sssata/fluxpad/APP/images/cal_key1_up.png

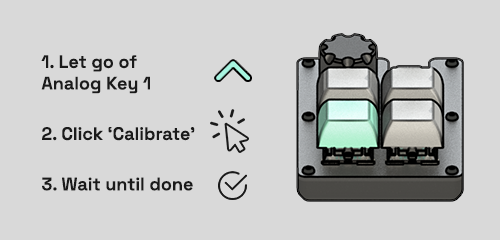
APP/images/cal_key1_up.png
