sssata/fluxpad/APP/images/cal_key2_down.png

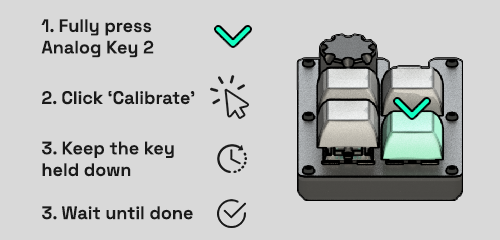
APP/images/cal_key2_down.png
