sssata/fluxpad/APP/images/cal_key2_up.png

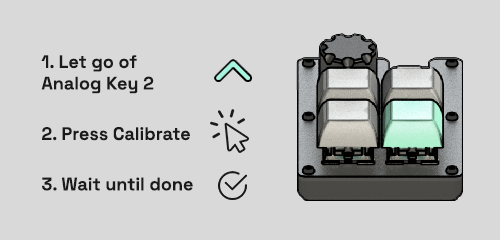
APP/images/cal_key2_up.png
