sssata/fluxpad/APP/images/cal_key3_down_2.png

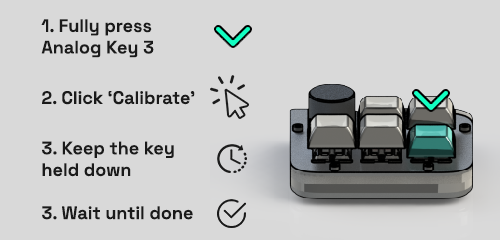
APP/images/cal_key3_down_2.png
