sssata/fluxpad/CAD/EE Export/302_PLATE.DXF

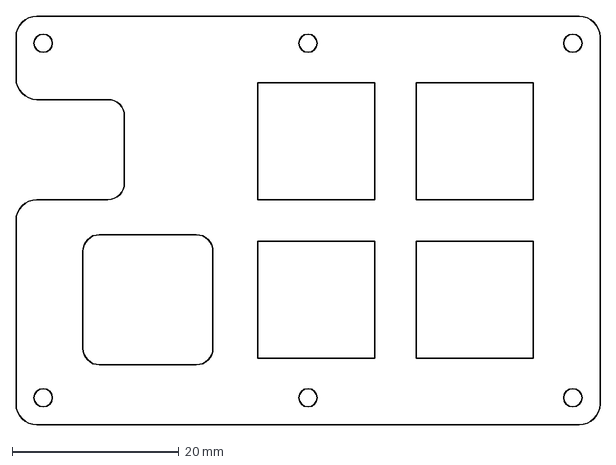
[picture p15: CAD file, 2023-02-28]
CAD/EE Export/302_PLATE.DXF
70.0 x 49.0 mm
