sssata/fluxpad/CAD/STL Export/101_HOUSING_B3.STL

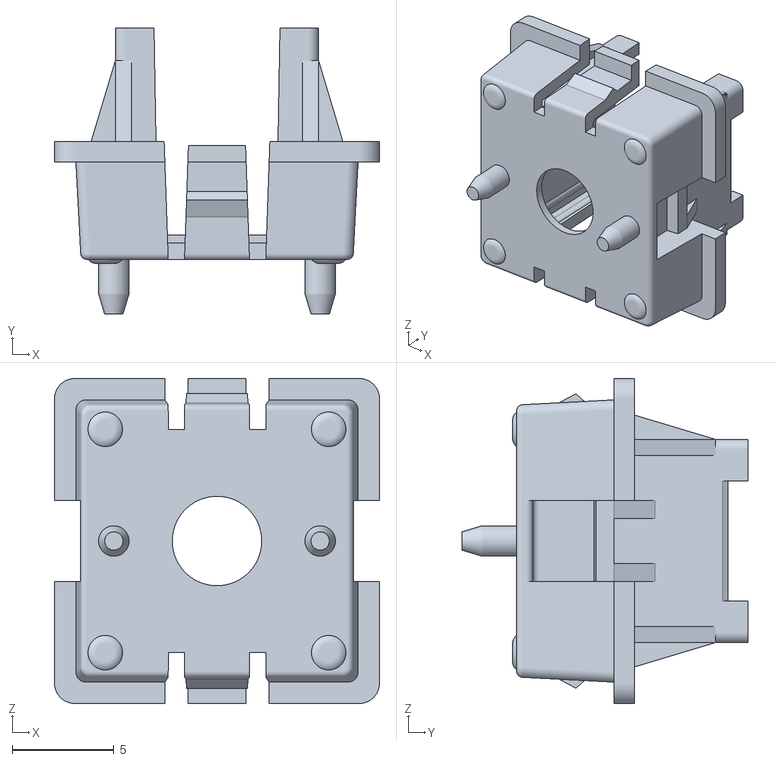
[picture p16: CAD file, 2023-02-28]
CAD/STL Export/101_HOUSING_B3.STL
16.0 x 14.1 x 16.0
