sssata/fluxpad/CAD/STL Export/Case Proto 5/111_KNOB.STL

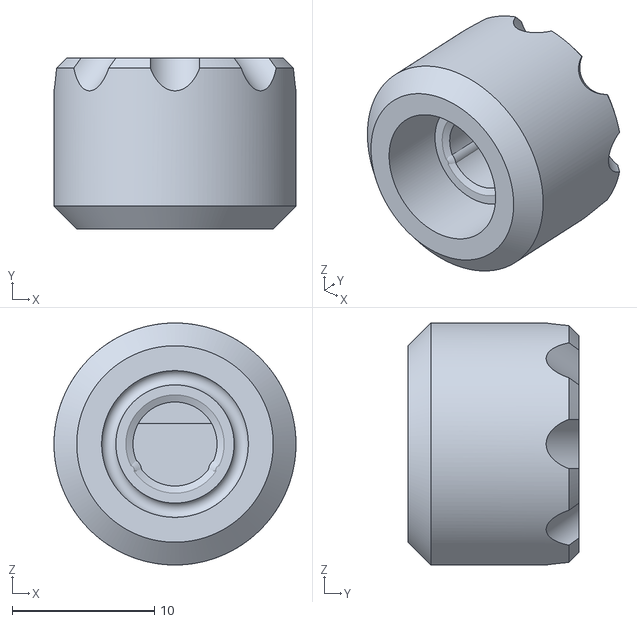
[picture p17: CAD file, 2023-03-26]
CAD/STL Export/Case Proto 5/111_KNOB.STL
17.0 x 12.0 x 17.0
