sssata/fluxpad/CAD/EE Export/301_PCB.DXF

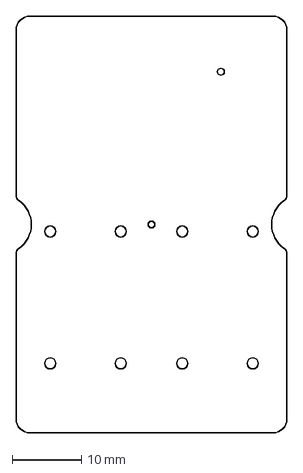
[picture p18: CAD file, 2023-02-28]
CAD/EE Export/301_PCB.DXF
39.0 x 60.0 mm
