sssata/fluxpad/CAD/STL Export/102_STEM_B3.STL

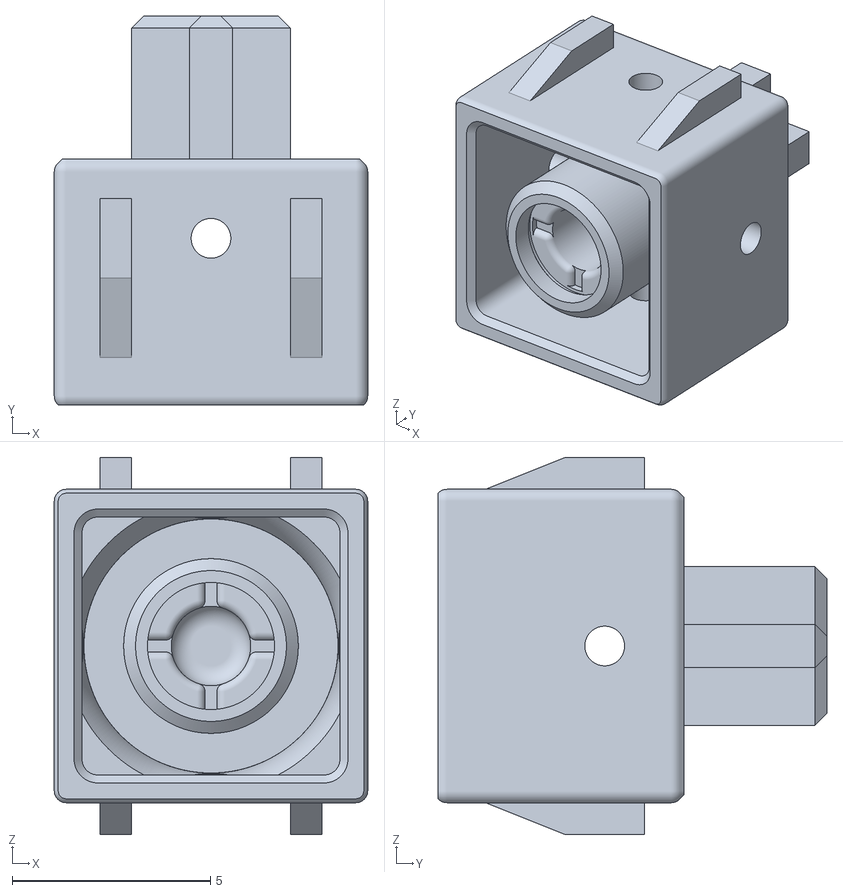
[picture p19: CAD file, 2023-02-28]
CAD/STL Export/102_STEM_B3.STL
7.90 x 9.80 x 9.50
