sssata/fluxpad/CAD/STL Export/Case Proto 1/110_CASE_A1.STL

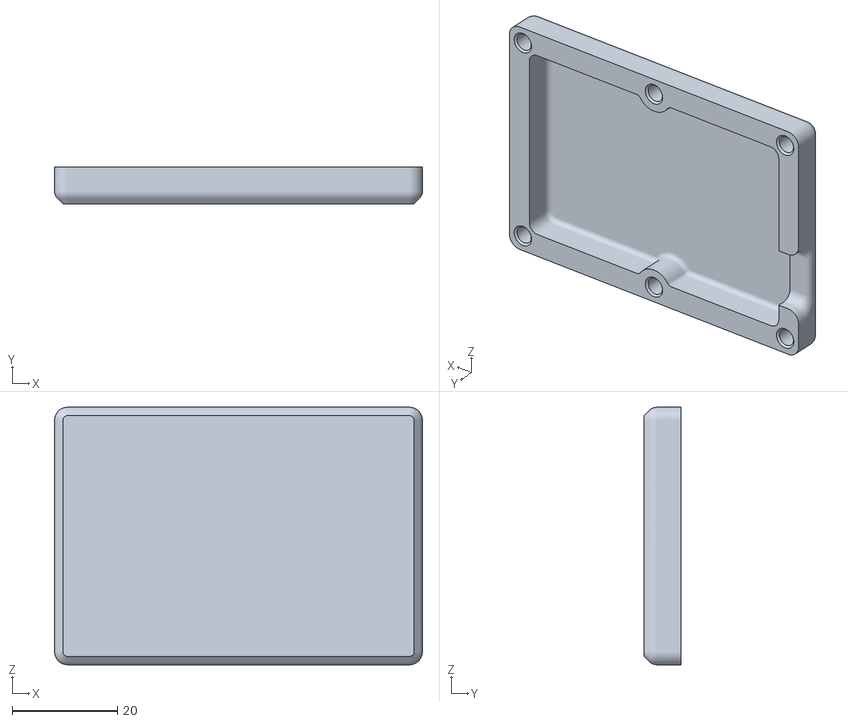
[picture p20: CAD file, 2023-02-28]
CAD/STL Export/Case Proto 1/110_CASE_A1.STL
70.0 x 7.00 x 49.0
