sssata/fluxpad/CAD/STL Export/Case Proto 2/302_PLATE.STL

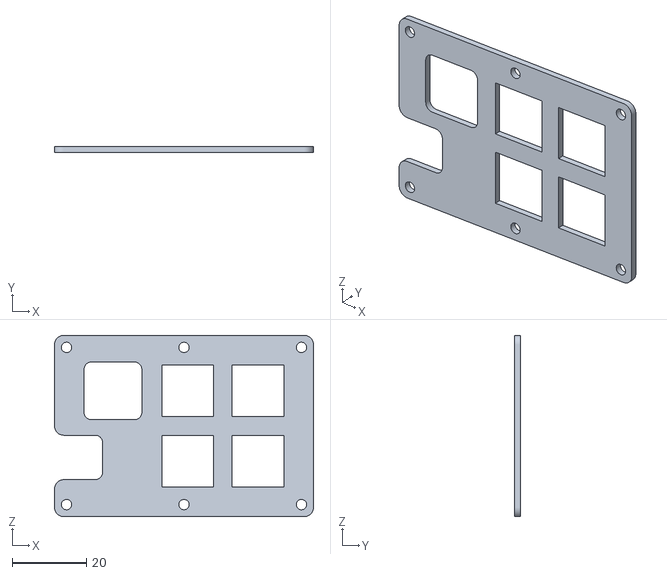
[picture p21: CAD file, 2023-02-20]
CAD/STL Export/Case Proto 2/302_PLATE.STL
70.0 x 1.60 x 49.0
