sssata/fluxpad/CAD/STL Export/901_DEMO_PLATE_B1.STL

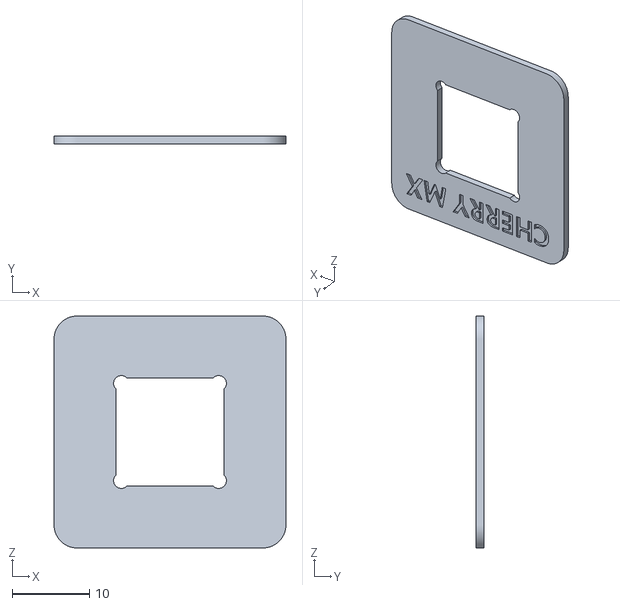
[picture p22: CAD file, 2023-02-28]
CAD/STL Export/901_DEMO_PLATE_B1.STL
30.0 x 1.00 x 30.0
