sssata/fluxpad/CAD/STL Export/Case Proto 2/112_SPACER.STL

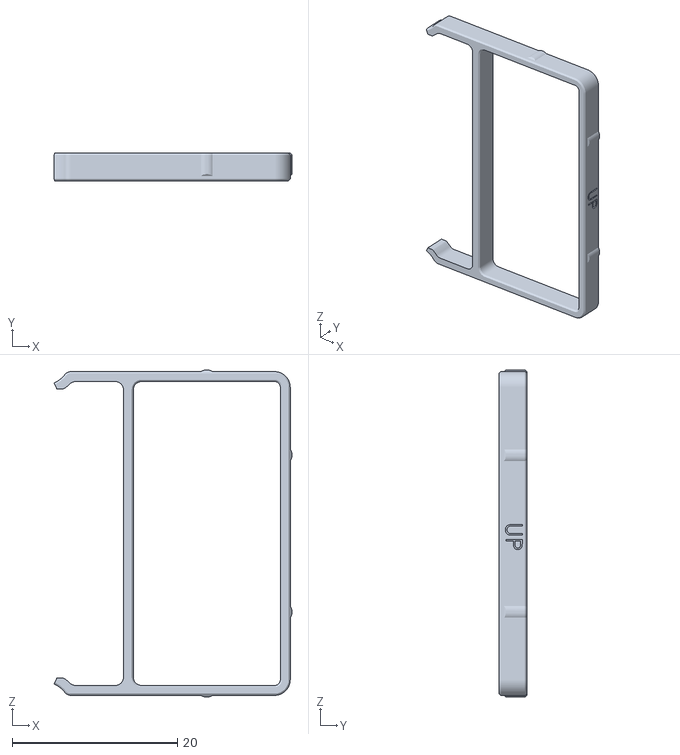
[picture p23: CAD file, 2023-02-20]
CAD/STL Export/Case Proto 2/112_SPACER.STL
28.8 x 3.35 x 39.6
