sssata/fluxpad/CAD/STL Export/103_COVER_A1.STL

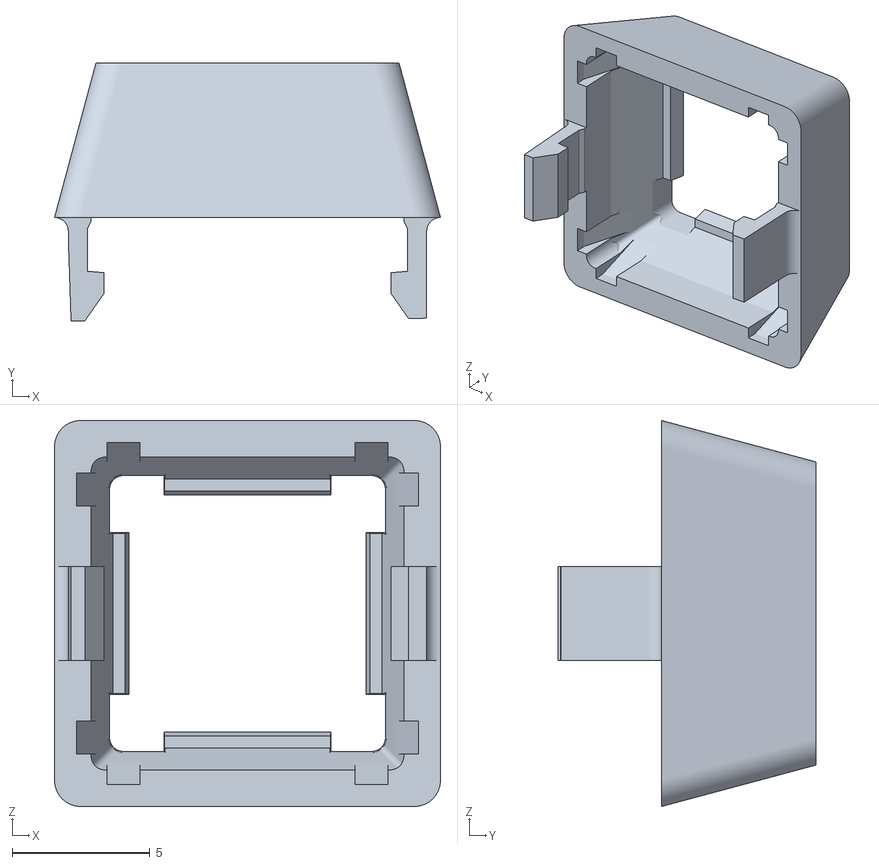
[picture p24: CAD file, 2023-02-28]
CAD/STL Export/103_COVER_A1.STL
14.0 x 9.35 x 14.0
