sssata/fluxpad/CAD/STL Export/901_DEMO_PCB_B1.STL

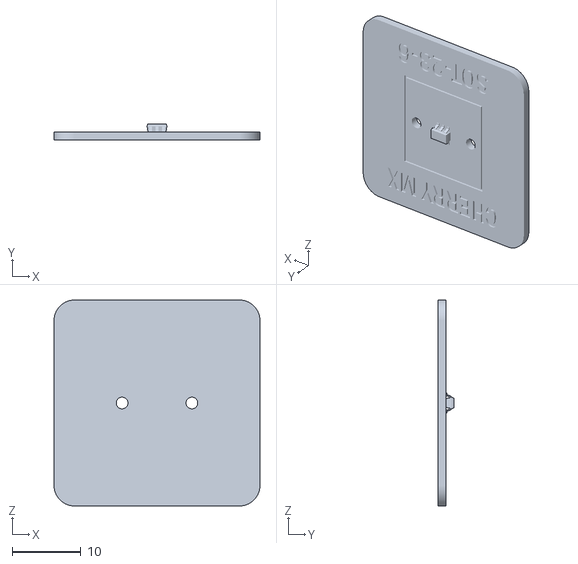
[picture p25: CAD file, 2023-02-28]
CAD/STL Export/901_DEMO_PCB_B1.STL
30.0 x 2.40 x 30.0
