sssata/fluxpad/CAD/STL Export/102_STEM_A1.STL

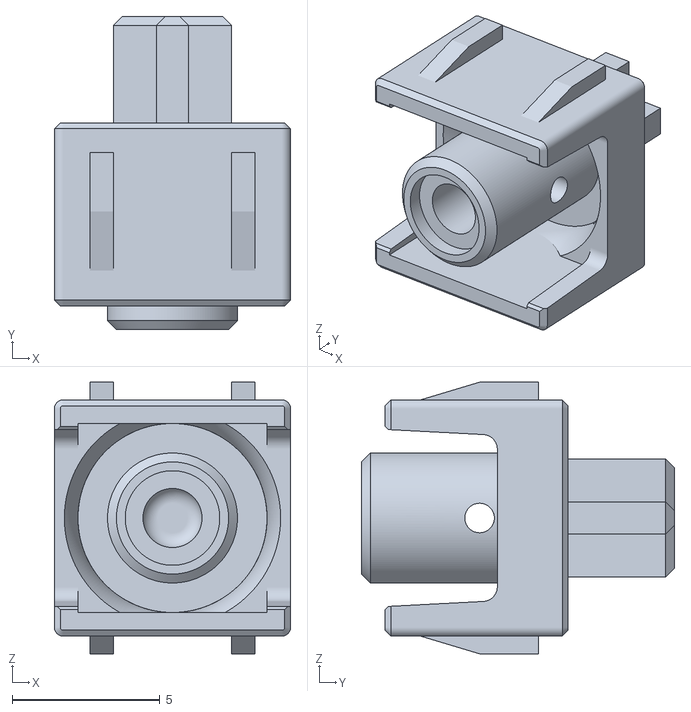
[picture p26: CAD file, 2023-02-28]
CAD/STL Export/102_STEM_A1.STL
8.00 x 10.6 x 9.20
