sssata/fluxpad/CAD/STL Export/901_DEMO_PCB_B2.STL

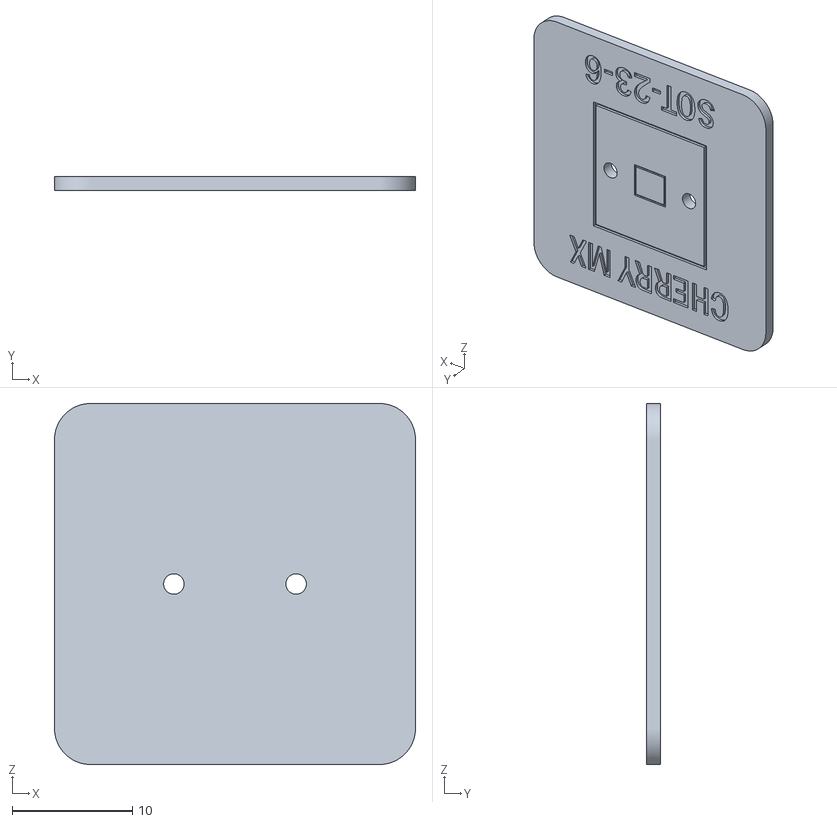
[picture p27: CAD file, 2023-02-28]
CAD/STL Export/901_DEMO_PCB_B2.STL
30.0 x 1.20 x 30.0
