sssata/fluxpad/CAD/STL Export/103_COVER_B3.STL

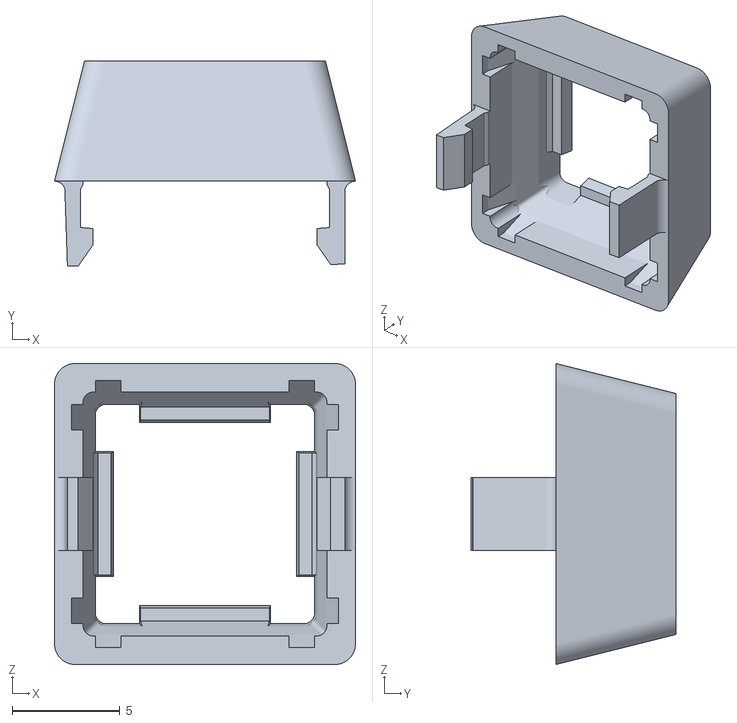
[picture p28: CAD file, 2023-02-28]
CAD/STL Export/103_COVER_B3.STL
14.0 x 9.55 x 14.0
