sssata/fluxpad/CAD/DSA_Keycap_CherryMX.step

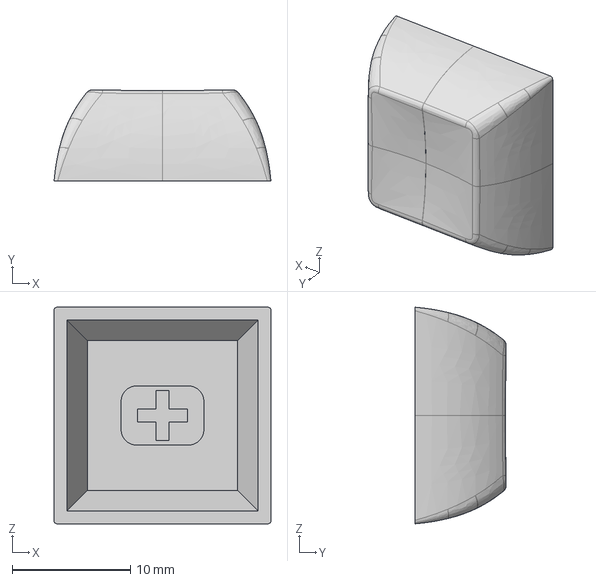
[picture p29: CAD file, 2023-03-06]
CAD/DSA_Keycap_CherryMX.step
18.3 x 7.69 x 18.3 mm
