sssata/fluxpad/CAD/LeeSpring-CI 012EG 02S.step

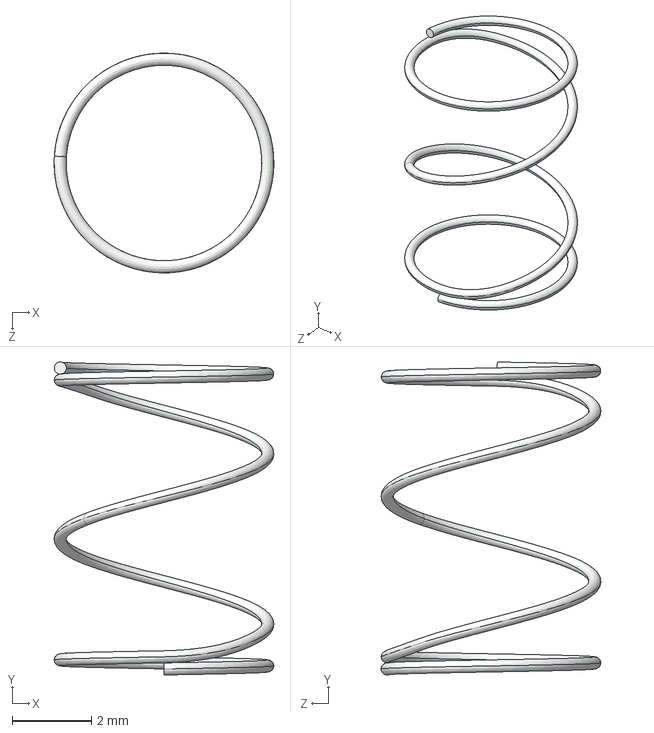
[picture p30: CAD file, 2023-02-28]
CAD/LeeSpring-CI 012EG 02S.step
5.54 x 7.88 x 5.54 mm
