sssata/fluxpad/CAD/PC016-240-6250-MW-0706-C-N-IN.stp

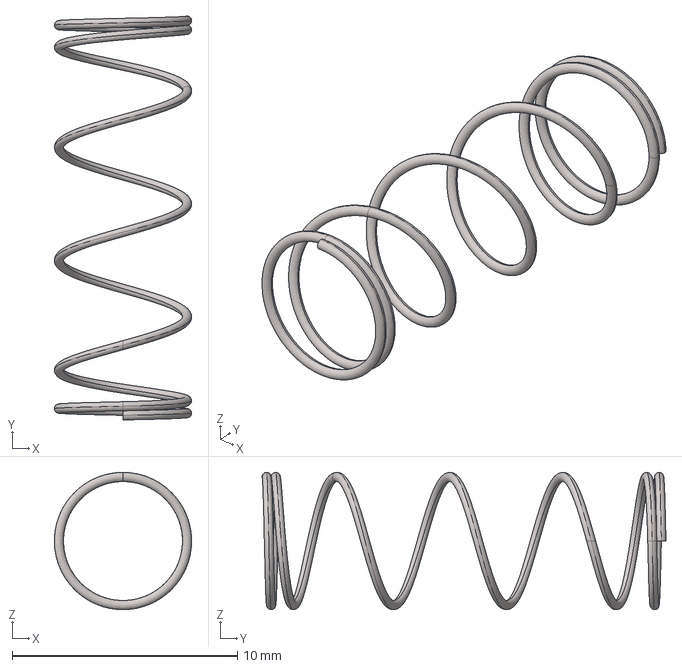
[picture p31: CAD file, 2023-02-28]
CAD/PC016-240-6250-MW-0706-C-N-IN.stp
6.10 x 17.9 x 6.09 mm
