sssata/fluxpad/ECAD/SimulationPlayground/SPICE Models/sglm009c/lmx24_lm2902-PSpiceFiles/SCHEMATIC1/transient/transient.cir

** Profile: "SCHEMATIC1-transient"  [ C:\Users\a0500607\Desktop\LMX24_LM2902_PSpice\lmx24_lm2902-pspicefiles\schematic1\transient.sim ] 

** Creating circuit file "transient.cir" 
** WARNING: THIS AUTOMATICALLY GENERATED FILE MAY BE OVERWRITTEN BY SUBSEQUENT SIMULATIONS

*Libraries: 
* Profile Libraries :
* Local Libraries :
.LIB "../../../lmx24_lm2902.lib" 
* From [PSPICE NETLIST] section of C:\cds_spb_home\cdssetup\OrCAD_PSpiceTIPSpice_Install\17.4.0\PSpice.ini file:
.lib "nom_pspti.lib" 
.lib "nom.lib" 

*Analysis directives: 
.TRAN  0 1m 0 
.OPTIONS ADVCONV
.OPTIONS FILEMODELSEARCH
.PROBE64 V(alias(*)) I(alias(*)) W(alias(*)) D(alias(*)) NOISE(alias(*)) 
.INC "..\SCHEMATIC1.net" 


.END
